HerrRiebmann/Caravan_Leveler/data/caravan.png

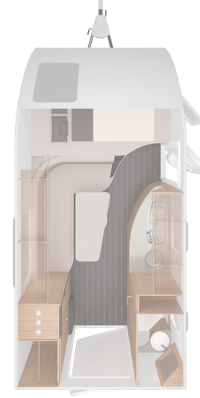
data/caravan.png
